NicklasVraa/OpenTinyHome/res/default-profile-pic.png

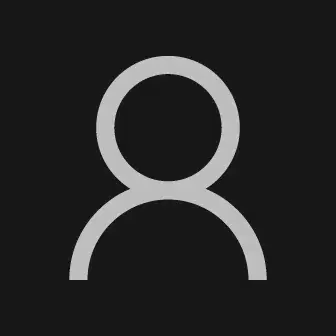
res/default-profile-pic.png
