NicklasVraa/OpenTinyHome/resources/images/inspect_output.png

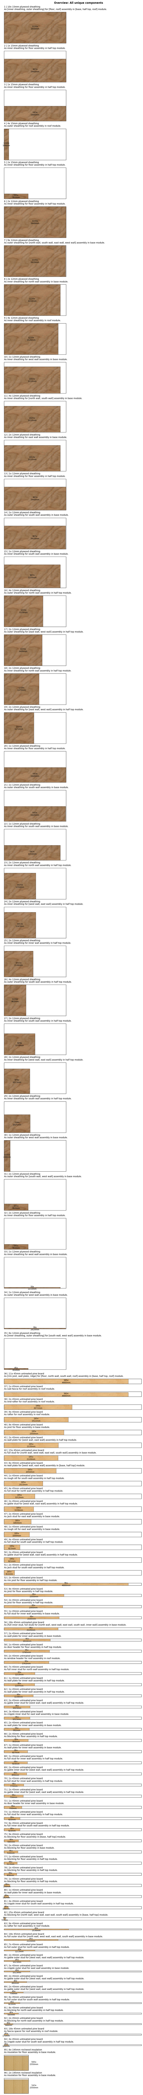
resources/images/inspect_output.png
