NicklasVraa/OpenTinyHome/resources/images/pack_output_1.png

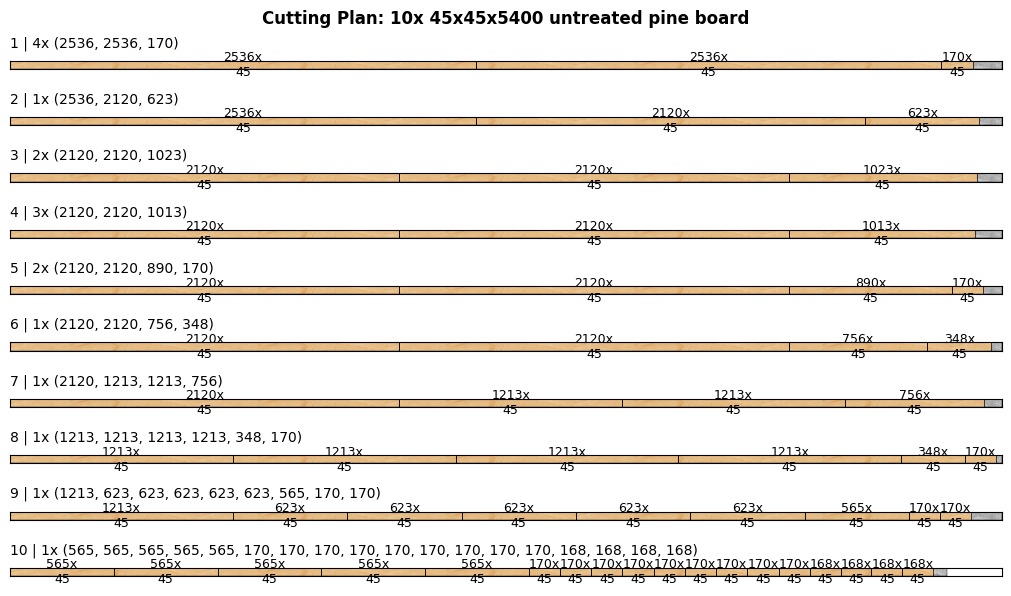
resources/images/pack_output_1.png
