NicklasVraa/OpenTinyHome/resources/images/pack_output_2.png

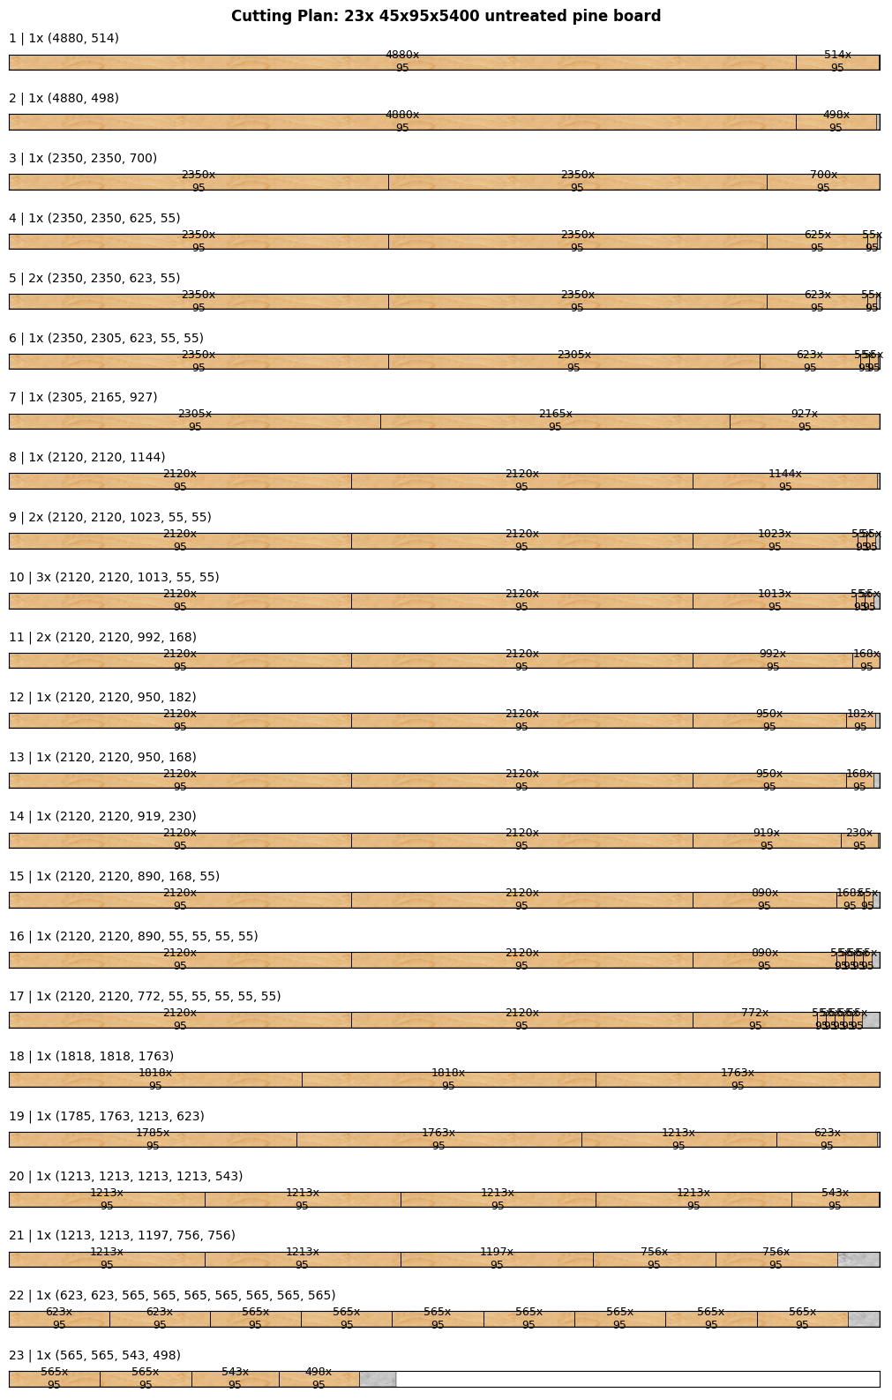
resources/images/pack_output_2.png
