NicklasVraa/OpenTinyHome/resources/images/pack_output_3.png

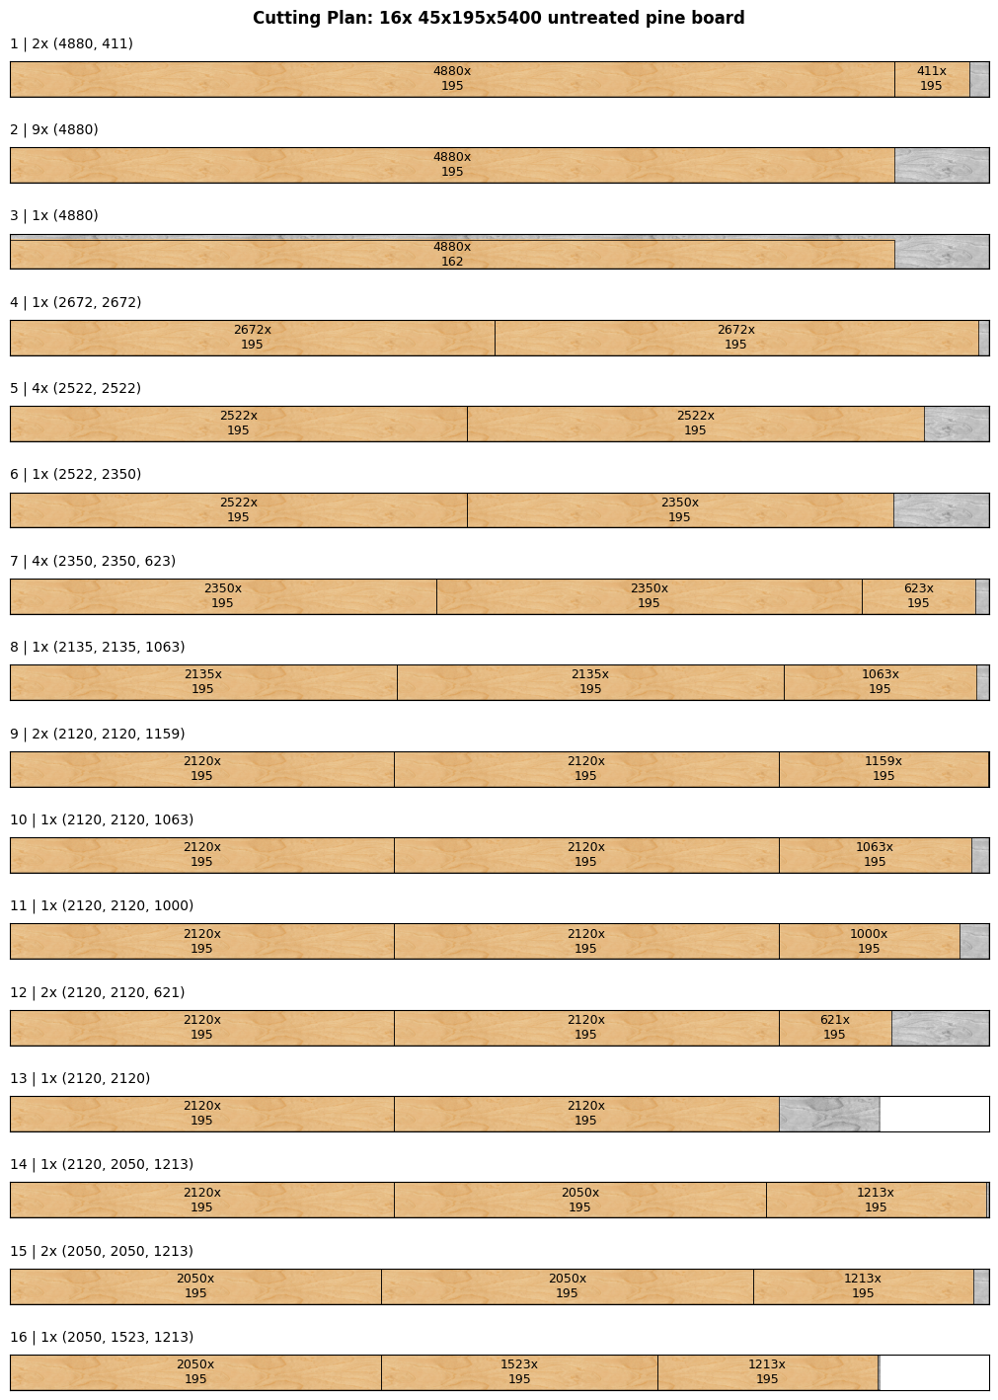
resources/images/pack_output_3.png
