NicklasVraa/OpenTinyHome/showcase/the_nano/images/img_0008.png

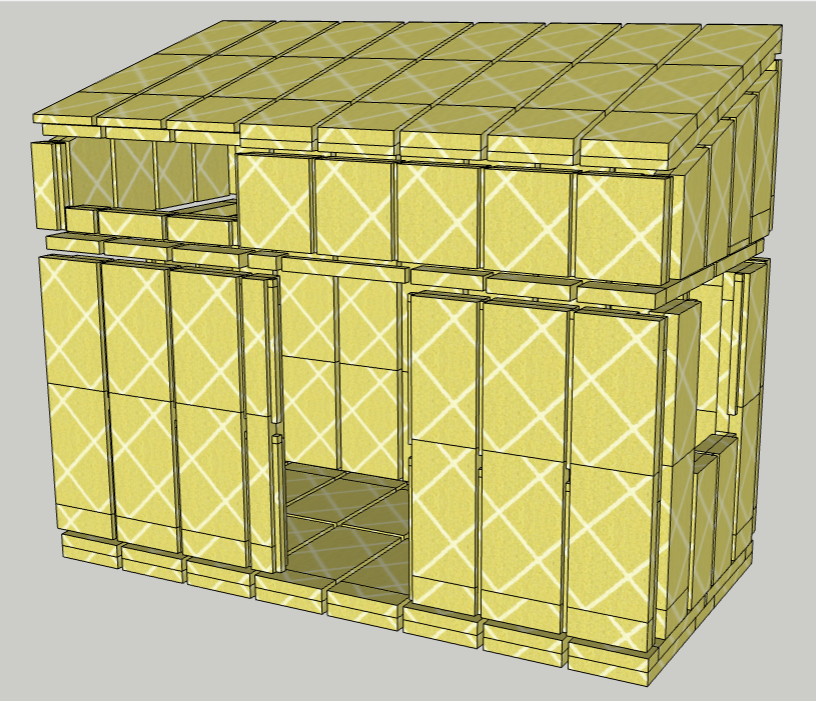
showcase/the_nano/images/img_0008.png
